timothy-s-dev/ok-to-wake-clock/include/display.h

#ifndef DISPLAY_H
#define DISPLAY_H

#include <Arduino.h>
#include <Wire.h>
#include <SparkFun_Alphanumeric_Display.h>

class Display {
public:
    static void init();
    static HT16K33& getInstance();
    static void setBrightness(uint8_t brightness);
};

#endif // DISPLAY_H
